nppc/TinyDiversityRX5808/Images/tVRX_bottom_top.jpg

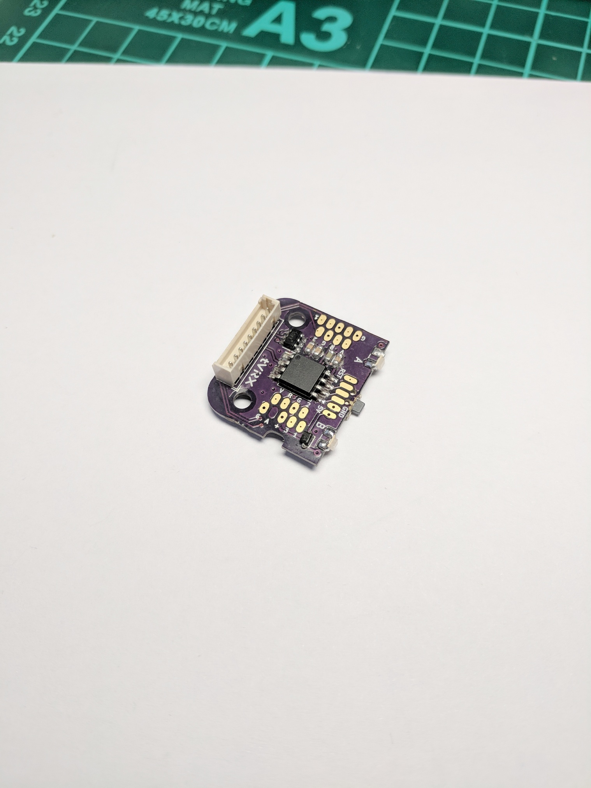
Images/tVRX_bottom_top.jpg
