nppc/TinyDiversityRX5808/Images/tVRX_Idea.png

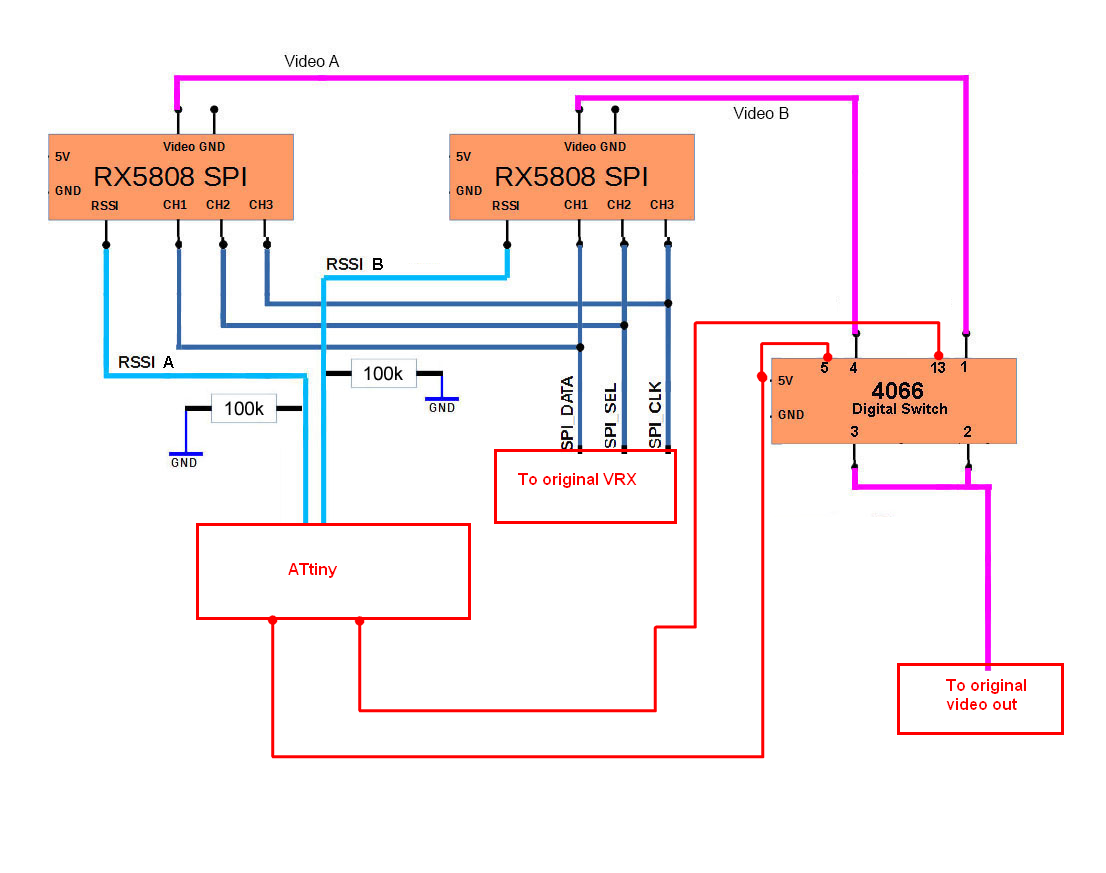
Images/tVRX_Idea.png
