nppc/TinyDiversityRX5808/Images/tVRX_left_receiver.jpg

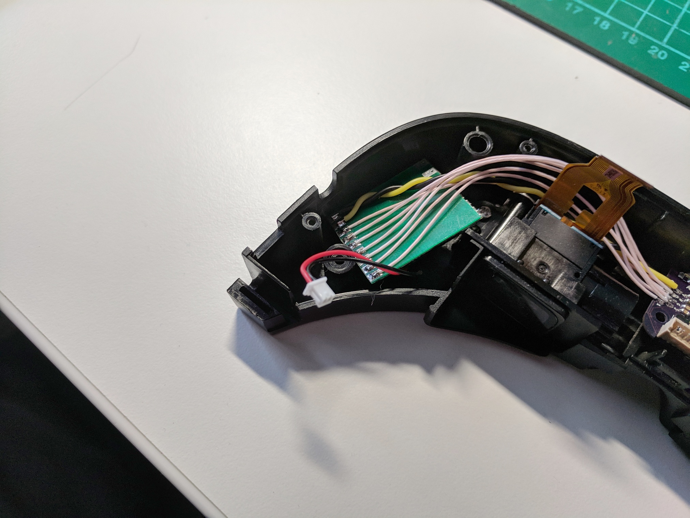
Images/tVRX_left_receiver.jpg
