nppc/TinyDiversityRX5808/Images/tVRX_rightAntennaConnection.jpg

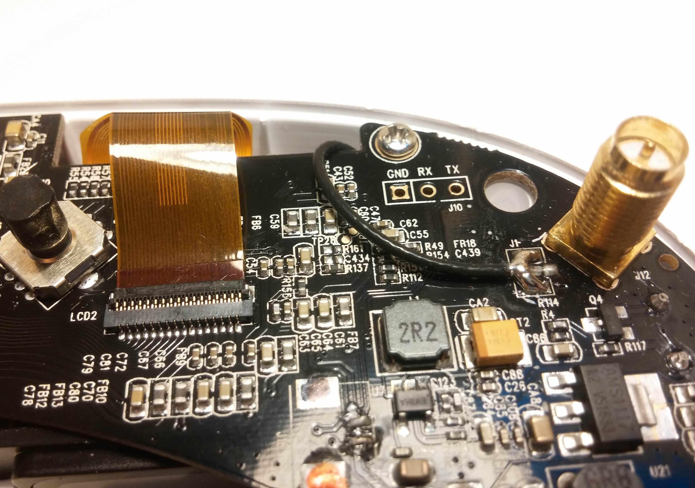
Images/tVRX_rightAntennaConnection.jpg
