nppc/TinyDiversityRX5808/Images/tVRX_ComponentsPlacement.jpg

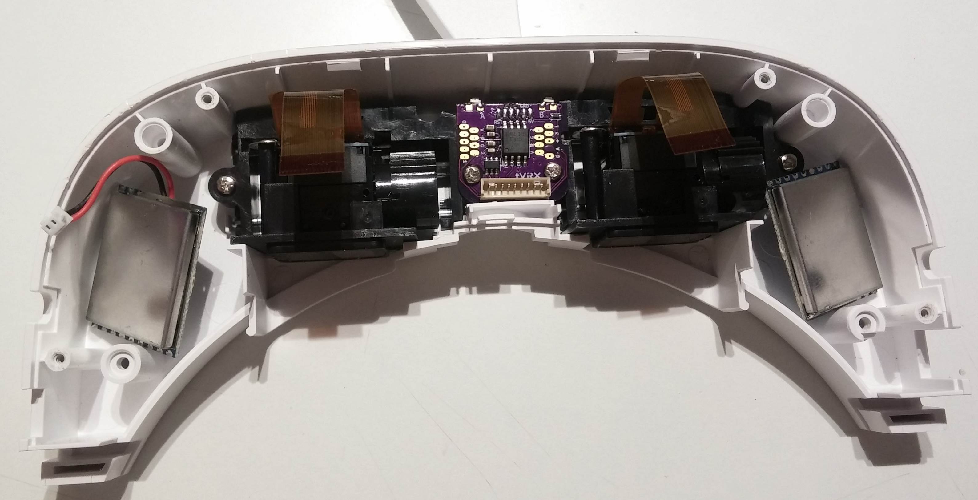
Images/tVRX_ComponentsPlacement.jpg
