nppc/TinyDiversityRX5808/Images/tVRX_assembled.jpg

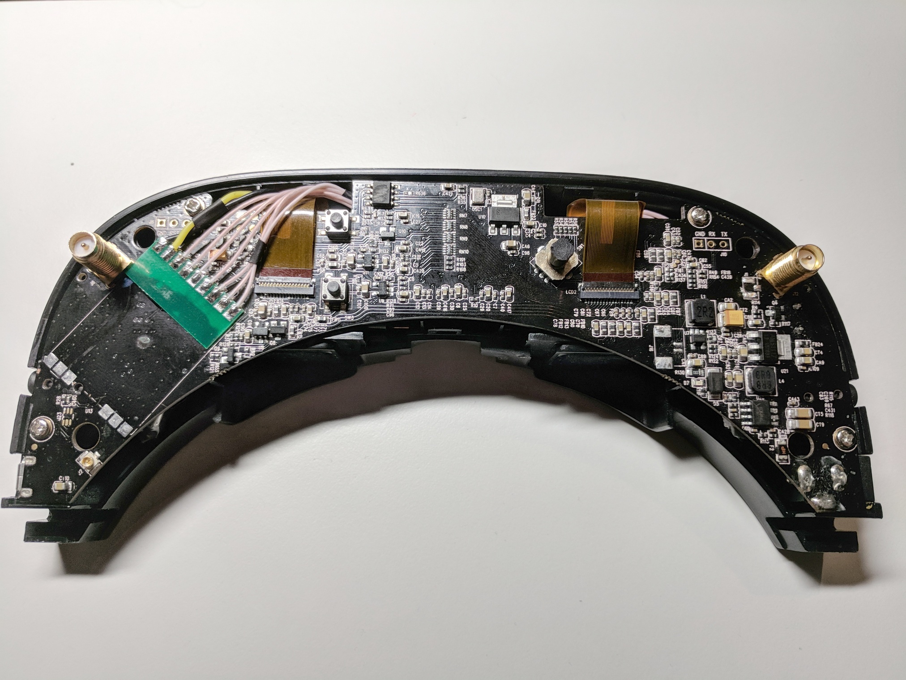
Images/tVRX_assembled.jpg
