nppc/TinyDiversityRX5808/Images/tVRX_soldered_bottom.jpg

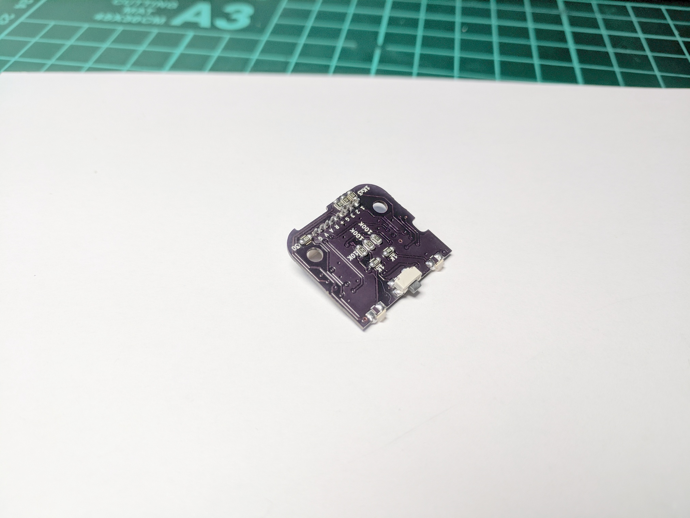
Images/tVRX_soldered_bottom.jpg
