nppc/TinyDiversityRX5808/Images/tVRX_soldering.jpg

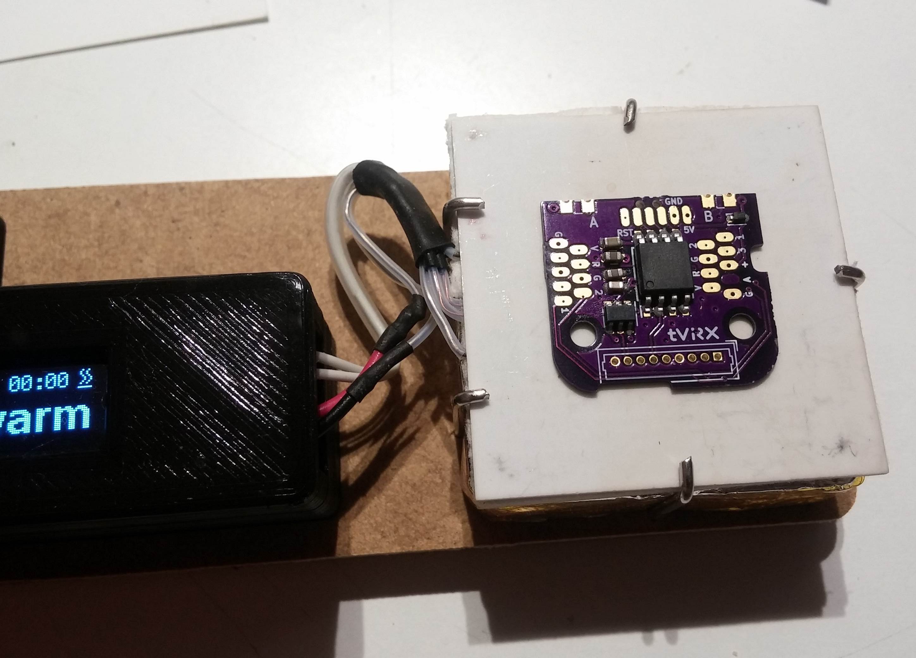
Images/tVRX_soldering.jpg
