nppc/TinyDiversityRX5808/Images/tVRX_testing.jpg

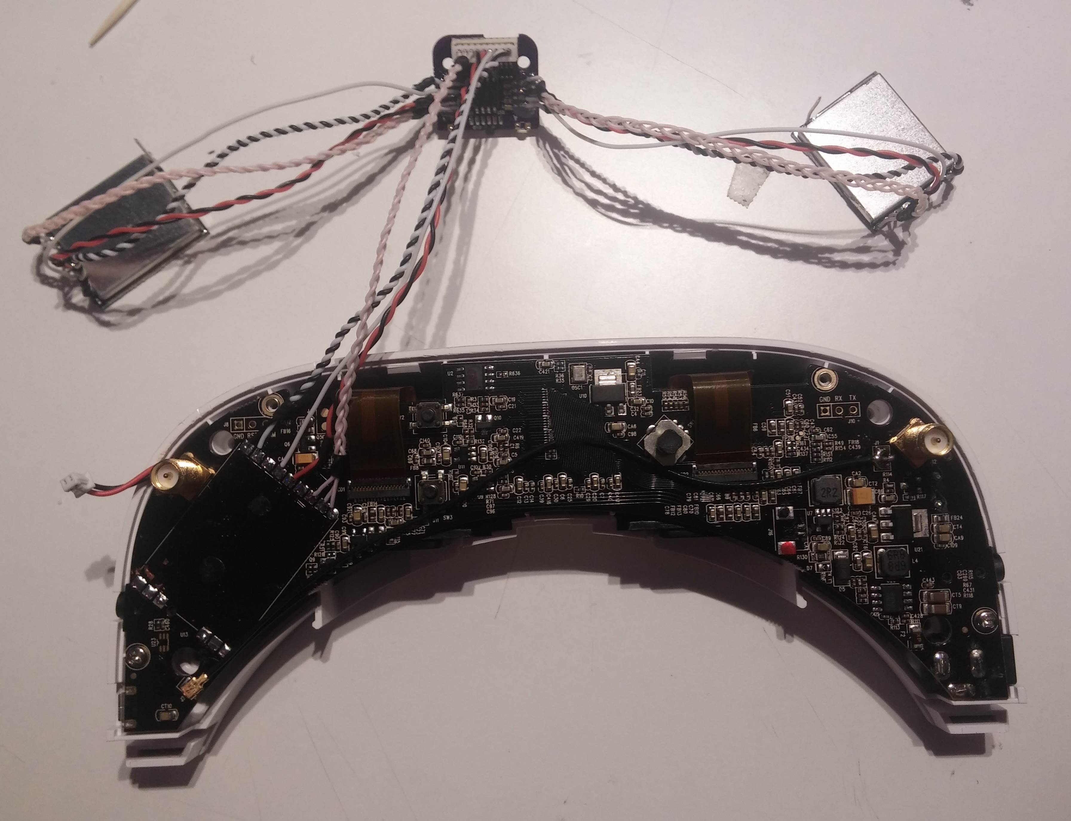
Images/tVRX_testing.jpg
